the-relentless-epee/Magnetic-Flux-Testing-Machine/Electronics/PCB Design Files/power board/power board.kicad_sch

## KiCad design Electronics/PCB Design Files/power board/power board.kicad_sch (2024-08-24)

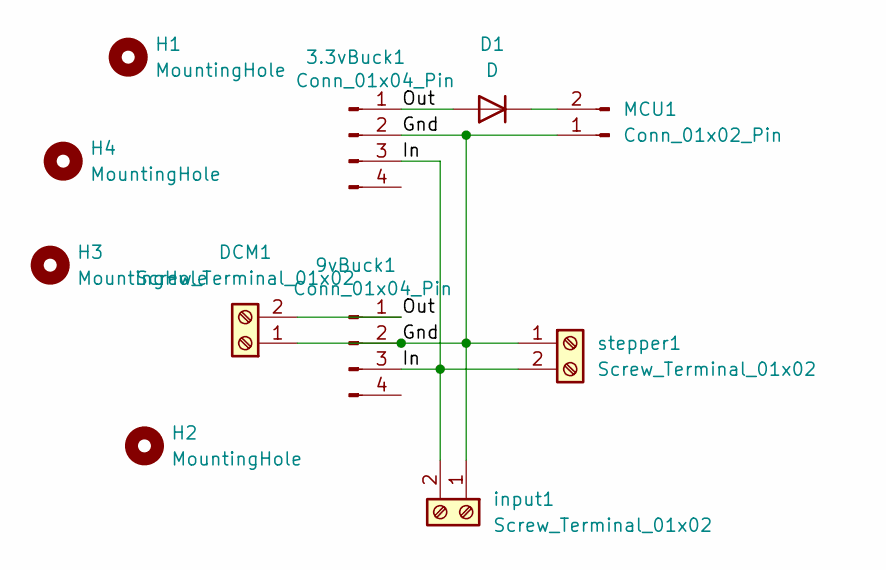
[picture p21: schematic power board.kicad_sch]

Parts:
3.3vBuck1, 9vBuck1: Conn_01x04_Pin; PinSocket_1x04_P2.54mm_Vertical
D1: D; D_A-405_P10.16mm_Horizontal
DCM1: Screw_Terminal_01x02; TerminalBlock_bornier-2_P5.08mm
H1, H2, H3, H4: MountingHole; MountingHole_3.2mm_M3
MCU1: Conn_01x02_Pin; PinSocket_1x02_P2.54mm_Vertical
input1: Screw_Terminal_01x02; TerminalBlock_bornier-2_P5.08mm
stepper1: Screw_Terminal_01x02; TerminalBlock_bornier-2_P5.08mm

Connections:
Gnd: 3.3vBuck1.2, 9vBuck1.2, DCM1.1, MCU1.1, input1.1, stepper1.1
In: 3.3vBuck1.3, 9vBuck1.3, input1.2, stepper1.2
unnamed: D1.1 (K), MCU1.2
Out: 3.3vBuck1.1, 9vBuck1.1, D1.2 (A), DCM1.2
